TiZed/Soldering_Plate/SolderPlate_FW/Core/Inc/config.h

/**
  ******************************************************************************
  * @file           : config.h
  * @author         : TiZed
  * @brief          : System configuration header
  ******************************************************************************
  * @attention
  *
  * Copyright (c) 2023 TiZed.
  * All rights reserved.
  *
  *
  ******************************************************************************
  */

#define MAX_TEMP 400.0          // Max. plate set temperature
#define MIN_TEMP 100.0          // Min. plate set temperature
#define DEFAULT_TEMP MIN_TEMP      // Default start temperature

#define THERM_R_T25     100000  // Thermistor 25C resistance, in ohms
#define THERM_BETA      3950    // Thermistor beta value

#define THERM_R1        4700    // Series resistor, in ohms
